rehmanis/DrugInjection/Pictures/GUI and Excel VBA/excel dictionary.JPG

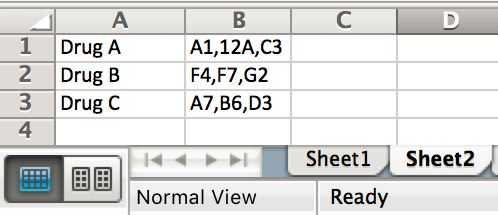
Pictures/GUI and Excel VBA/excel dictionary.JPG
