rehmanis/DrugInjection/Mech Design/Plate to slides connector/rev1.2/slide to slide connector part B rev1.2.SLDPRT

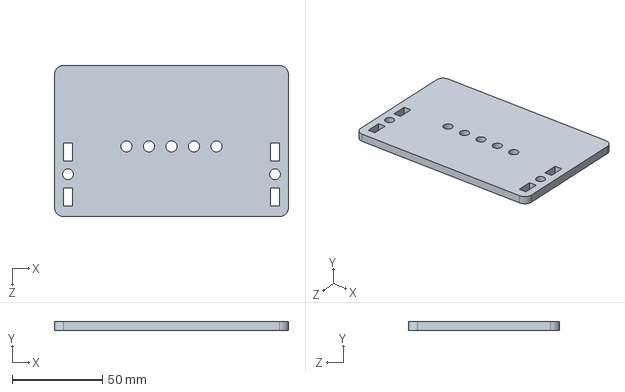
[picture p44: CAD file, 2016-05-08, last stored version]
Mech Design/Plate to slides connector/rev1.2/slide to slide connector part B rev1.2.SLDPRT
130.0 x 5.00 x 84.0 mm
