rehmanis/DrugInjection/Mech Design/Melles Griot/stage.SLDPRT

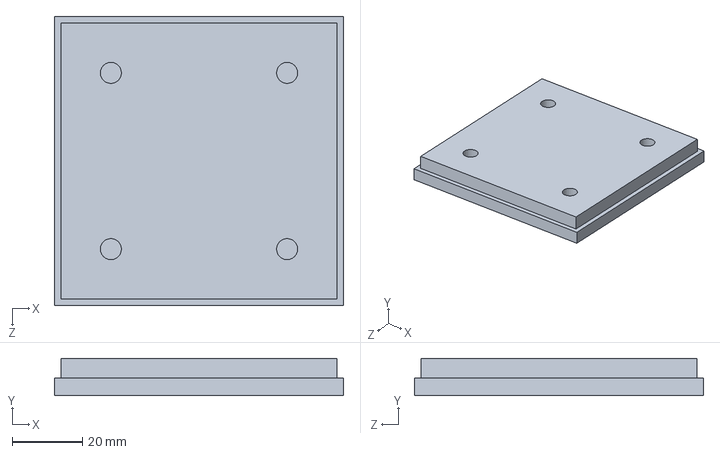
[picture p46: CAD file, 2016-05-08, last stored version]
Mech Design/Melles Griot/stage.SLDPRT
82.0 x 10.5 x 82.0 mm
