rehmanis/DrugInjection/Mech Design/Plate to slides connector/rev1.2/stage connecting plate rev1.2.SLDPRT

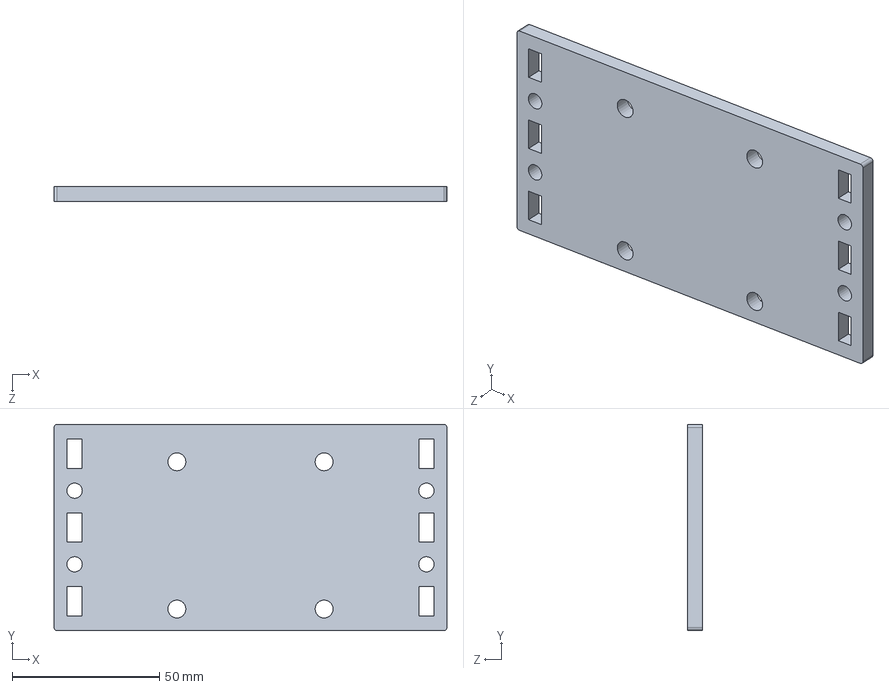
[picture p47: CAD file, 2016-05-08, last stored version]
Mech Design/Plate to slides connector/rev1.2/stage connecting plate rev1.2.SLDPRT
133.5 x 70.0 x 5.00 mm
