rehmanis/DrugInjection/Mech Design/96 well microplate securement/top plate bottom part.SLDPRT

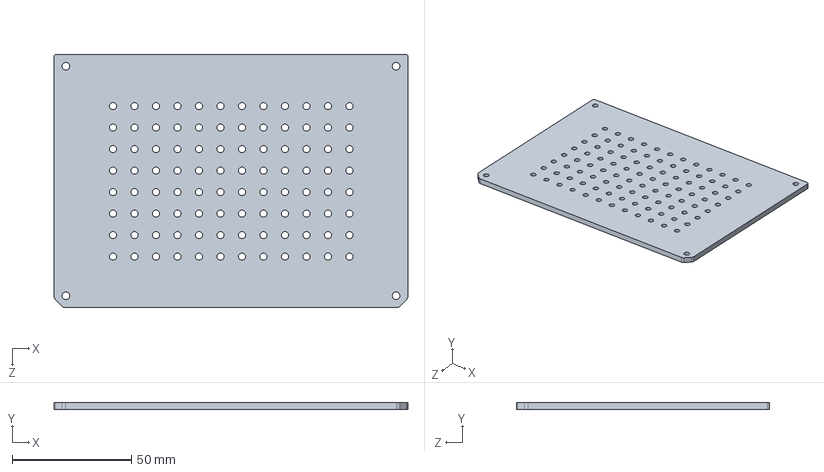
[picture p48: CAD file, 2016-05-08, last stored version]
Mech Design/96 well microplate securement/top plate bottom part.SLDPRT
148.2 x 3.00 x 106.1 mm
