rehmanis/DrugInjection/Mech Design/Plate to slides connector/rev1.2/L-connector rev1.2.SLDPRT

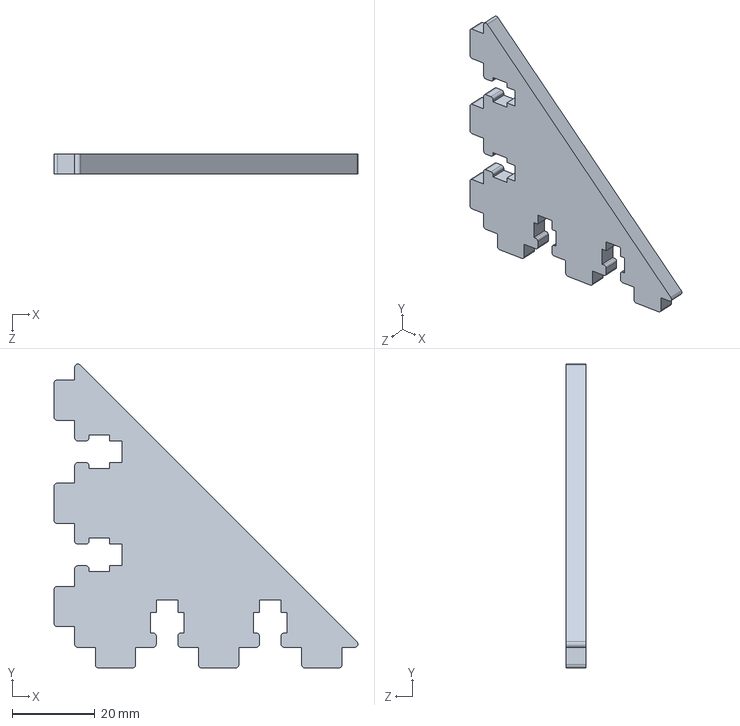
[picture p49: CAD file, 2016-05-08, last stored version]
Mech Design/Plate to slides connector/rev1.2/L-connector rev1.2.SLDPRT
73.7 x 73.7 x 4.95 mm
