rehmanis/DrugInjection/Mech Design/Plate to slides connector/rev1.2/well securing base plate rev1.2.SLDPRT

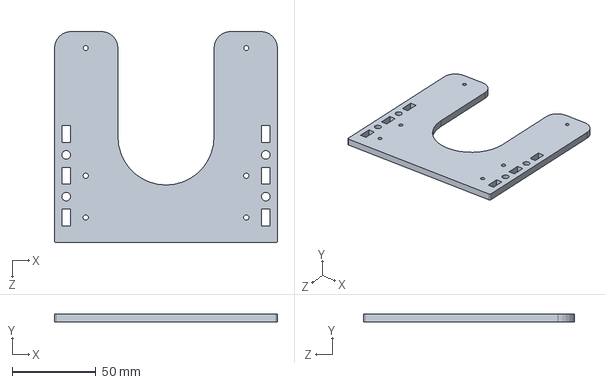
[picture p50: CAD file, 2016-05-08, last stored version]
Mech Design/Plate to slides connector/rev1.2/well securing base plate rev1.2.SLDPRT
133.5 x 5.00 x 126.4 mm
