rehmanis/DrugInjection/Mech Design/96 well microplate securement/PDMS layer.SLDPRT

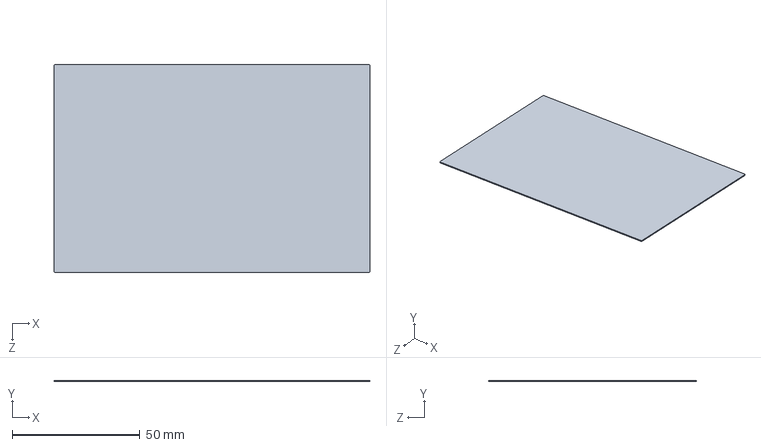
[picture p52: CAD file, 2016-05-08, last stored version]
Mech Design/96 well microplate securement/PDMS layer.SLDPRT
123.5 x 0.5 x 81.2 mm
