rehmanis/DrugInjection/Mech Design/96 well securement initial ideas/top_frame_v5.SLDPRT

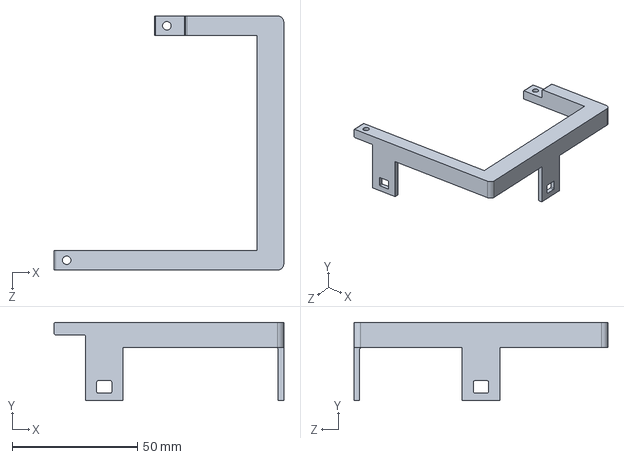
[picture p53: CAD file, 2016-05-08, last stored version]
Mech Design/96 well securement initial ideas/top_frame_v5.SLDPRT
91.7 x 31.3 x 101.4 mm
