rehmanis/DrugInjection/Mech Design/96 well securement initial ideas/Base plate_scaled_down.SLDPRT

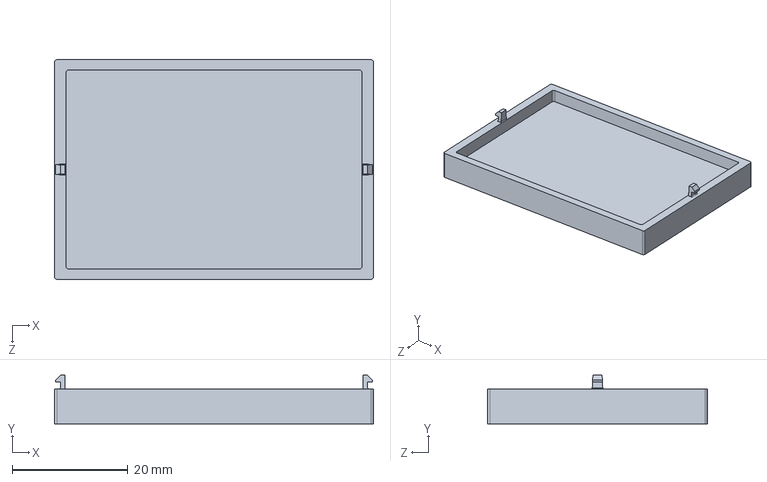
[picture p55: CAD file, 2016-05-08, last stored version]
Mech Design/96 well securement initial ideas/Base plate_scaled_down.SLDPRT
55.2 x 8.40 x 38.0 mm
