rehmanis/DrugInjection/Mech Design/96 well securement initial ideas/top_frame_scaled_down.SLDPRT

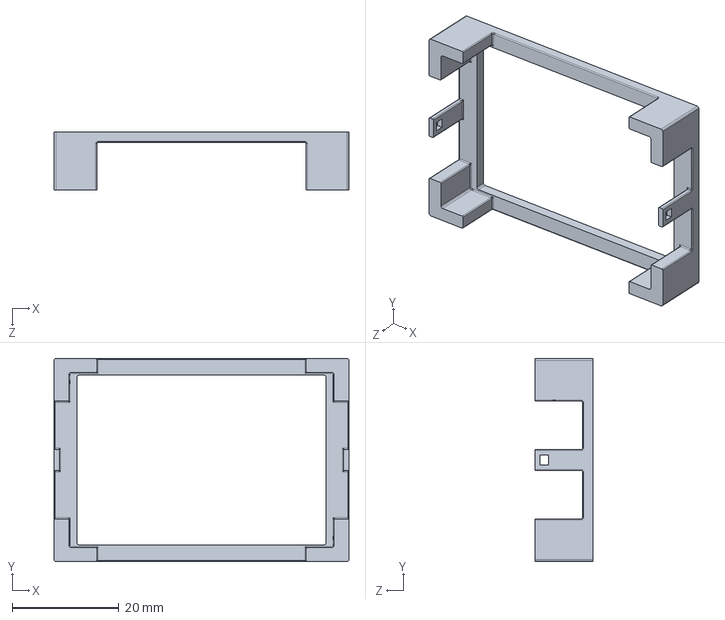
[picture p56: CAD file, 2016-05-08, last stored version]
Mech Design/96 well securement initial ideas/top_frame_scaled_down.SLDPRT
55.2 x 38.0 x 10.9 mm
