rehmanis/DrugInjection/Mech Design/Mech Design/96 well securement initial ideas/Part2.sldprt

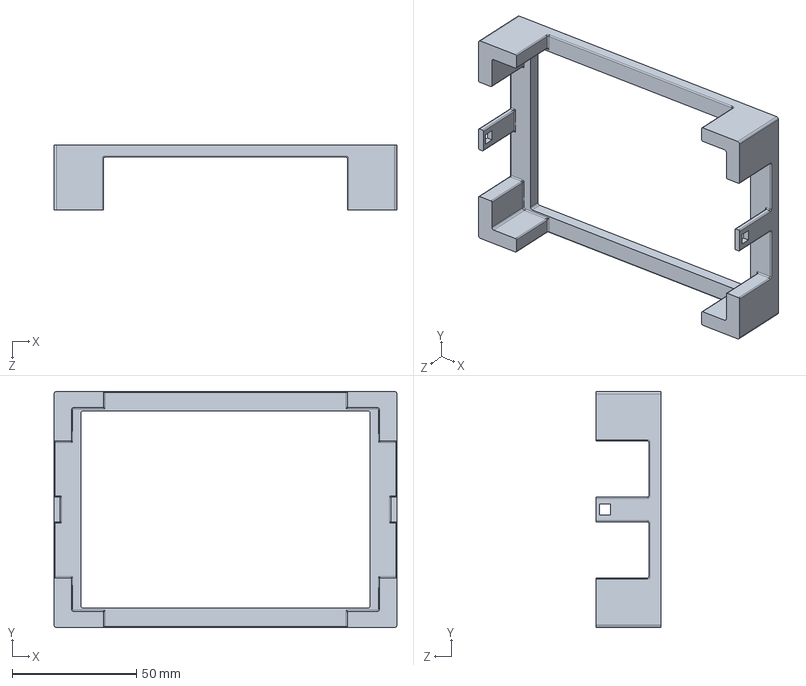
[picture p57: CAD file, 2016-05-08, last stored version]
Mech Design/Mech Design/96 well securement initial ideas/Part2.sldprt
138.0 x 95.0 x 26.3 mm
