rehmanis/DrugInjection/Mech Design/96 well securement initial ideas/Base plate_part2_v5.SLDPRT

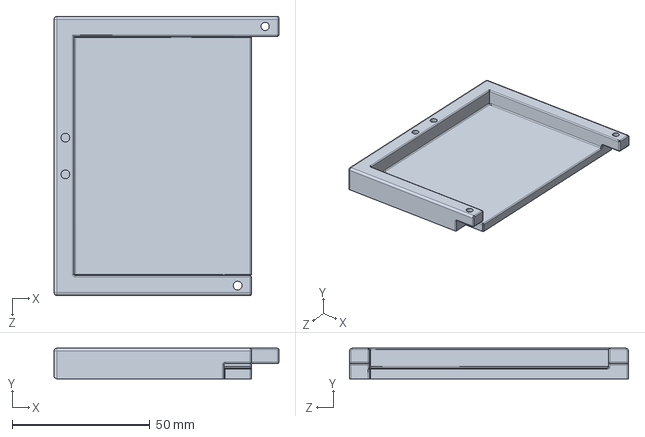
[picture p58: CAD file, 2016-05-08, last stored version]
Mech Design/96 well securement initial ideas/Base plate_part2_v5.SLDPRT
81.7 x 11.1 x 101.4 mm
