rehmanis/DrugInjection/Mech Design/96 well securement initial ideas/Part1.sldprt

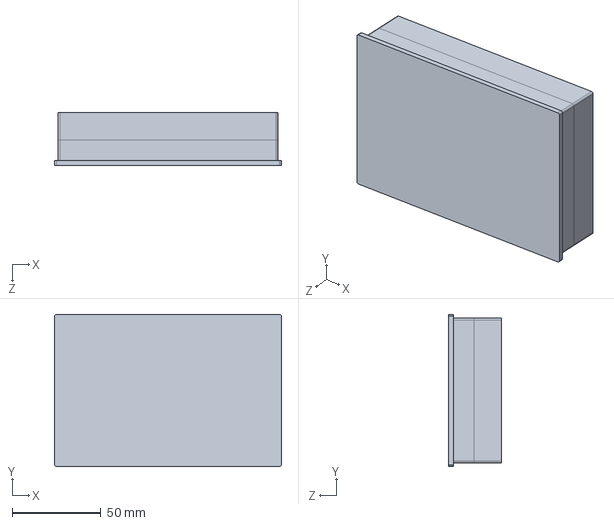
[picture p59: CAD file, 2016-05-08, last stored version]
Mech Design/96 well securement initial ideas/Part1.sldprt
127.6 x 85.5 x 29.8 mm
