rehmanis/DrugInjection/Mech Design/96 well securement initial ideas/snaps.SLDPRT

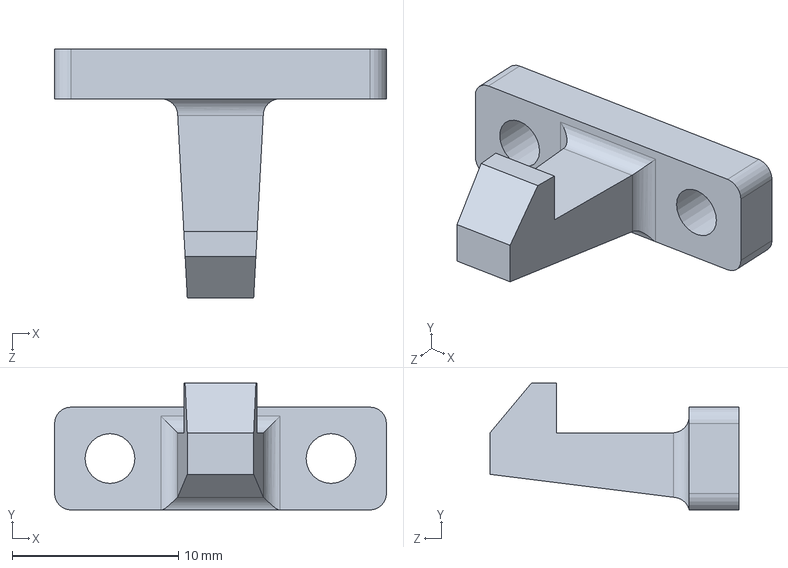
[picture p60: CAD file, 2016-05-08, last stored version]
Mech Design/96 well securement initial ideas/snaps.SLDPRT
20.0 x 7.65 x 15.0 mm
