rehmanis/DrugInjection/Mech Design/96 well securement initial ideas/Base plate.SLDPRT

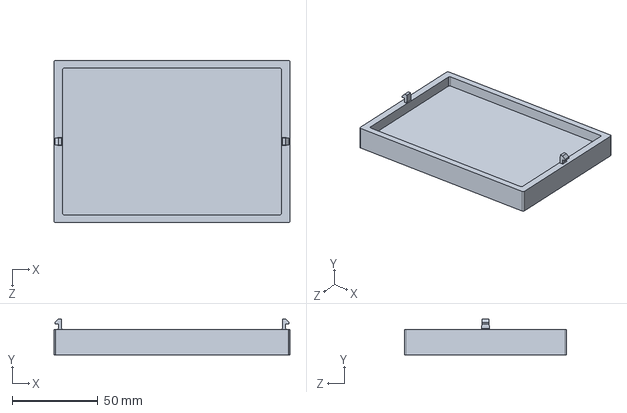
[picture p61: CAD file, 2016-05-08, last stored version]
Mech Design/96 well securement initial ideas/Base plate.SLDPRT
138.0 x 21.0 x 95.0 mm
