rehmanis/DrugInjection/Mech Design/96 well securement initial ideas/snaps_v3.SLDPRT

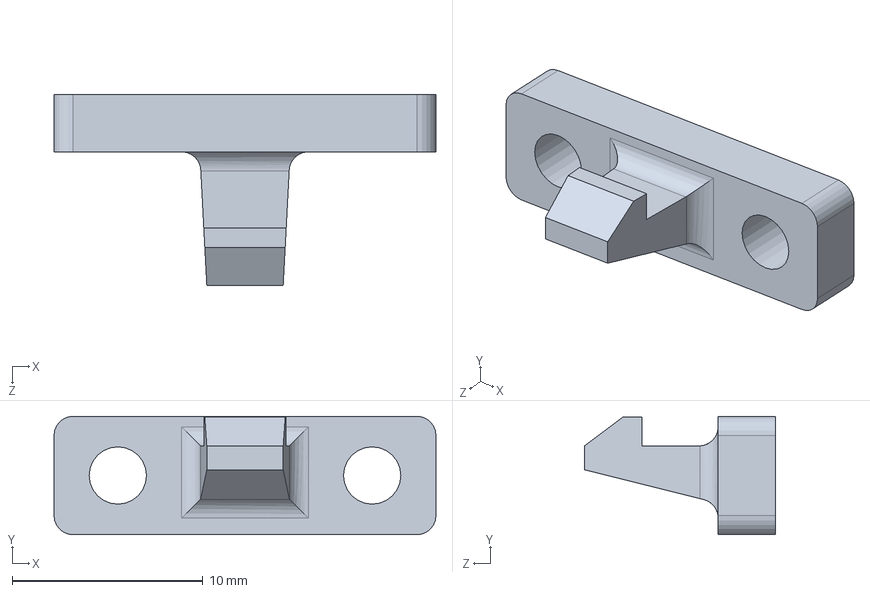
[picture p62: CAD file, 2016-05-08, last stored version]
Mech Design/96 well securement initial ideas/snaps_v3.SLDPRT
20.0 x 6.20 x 10.0 mm
