rehmanis/DrugInjection/Mech Design/96 well securement initial ideas/top_frame.SLDPRT

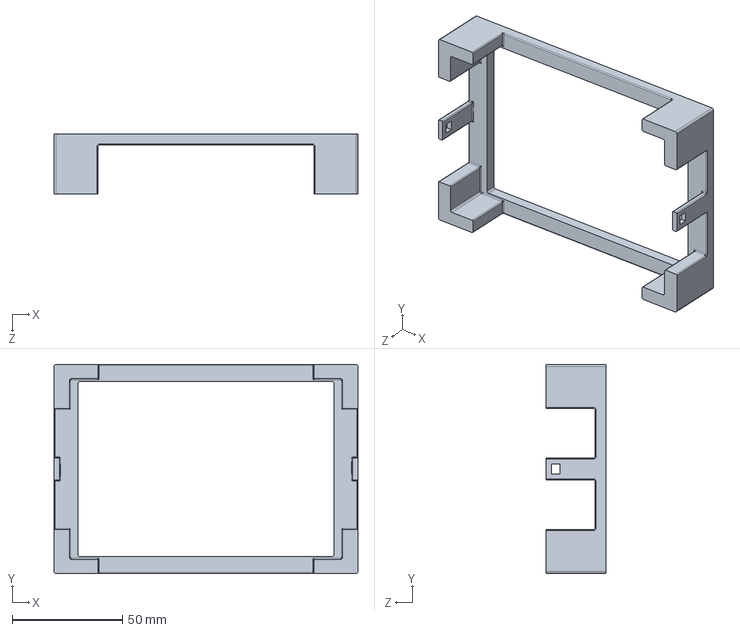
[picture p63: CAD file, 2016-05-08, last stored version]
Mech Design/96 well securement initial ideas/top_frame.SLDPRT
138.0 x 95.0 x 27.3 mm
